OBJEX-Labs/Smart-DoorWindow-sensor/ESP32-C3 Version/Simulations & Tests/DS1Z_QuickPrint19.png

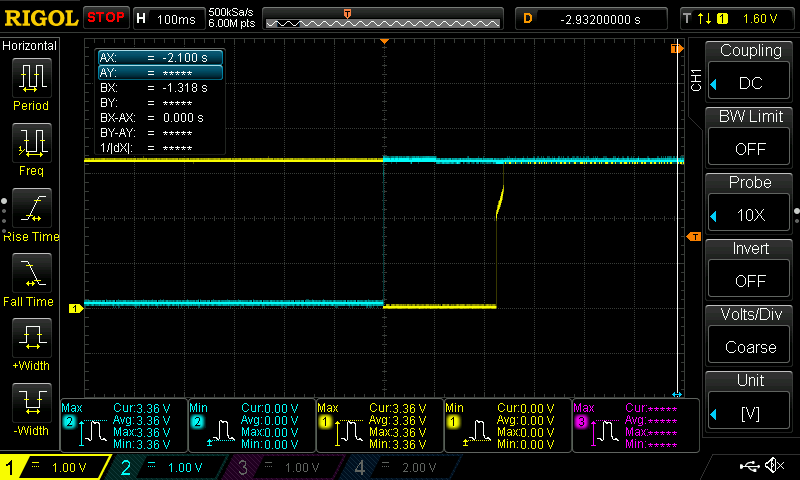
ESP32-C3 Version/Simulations & Tests/DS1Z_QuickPrint19.png
